MbFredys/RGB-LED-and-High-Dencity-CCT-Controller/Release/3D-pro.png

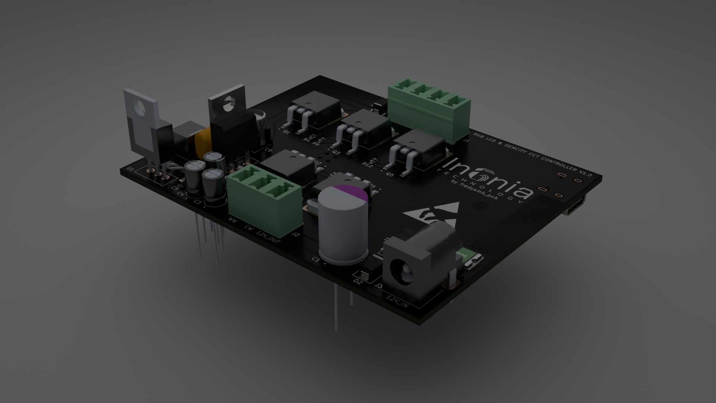
Release/3D-pro.png
