MbFredys/RGB-LED-and-High-Dencity-CCT-Controller/Manufacturing/bottom.png

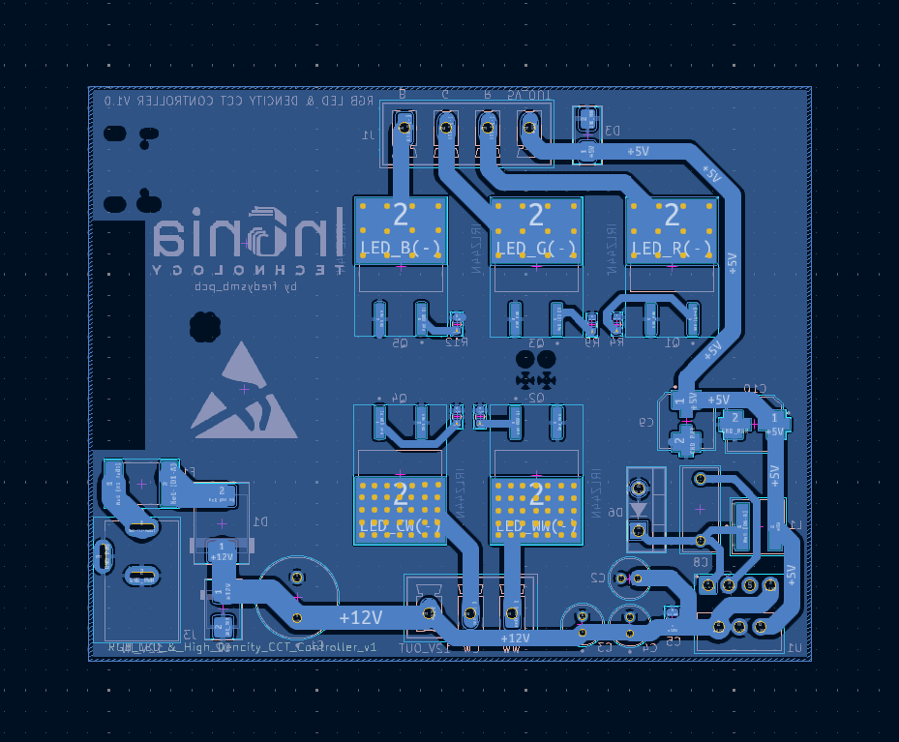
Manufacturing/bottom.png
