MbFredys/RGB-LED-and-High-Dencity-CCT-Controller/Manufacturing/top.png

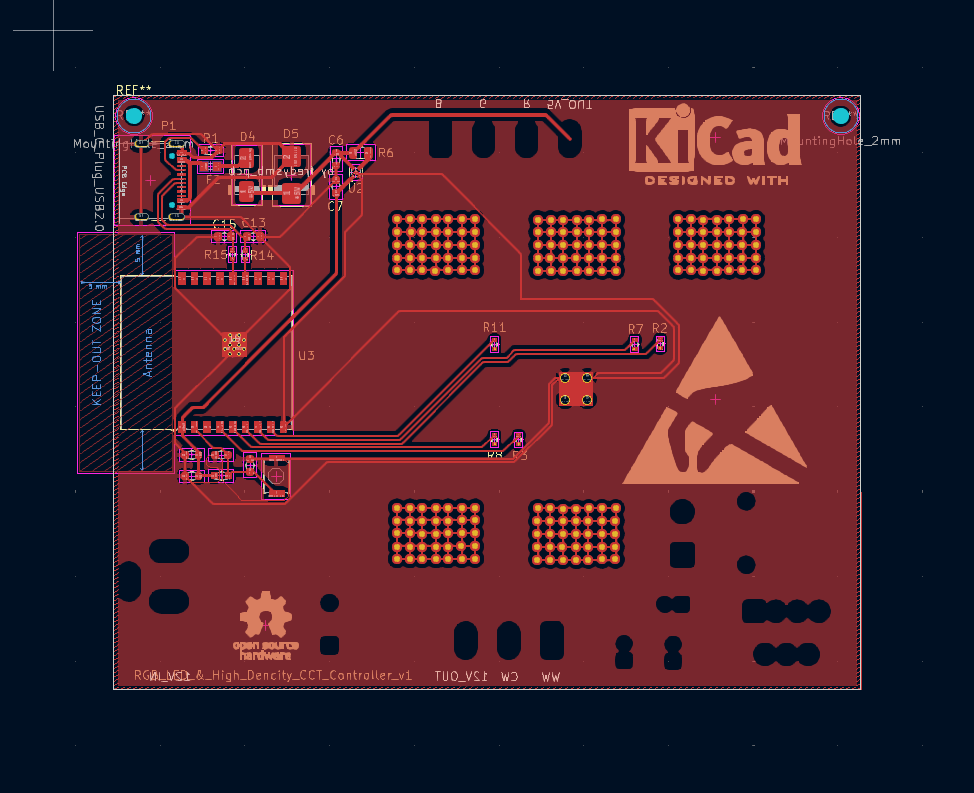
Manufacturing/top.png
